r0hitrajesh/arys-rohitrajesh-footpeg-fea/CAD/v1 Top View.png

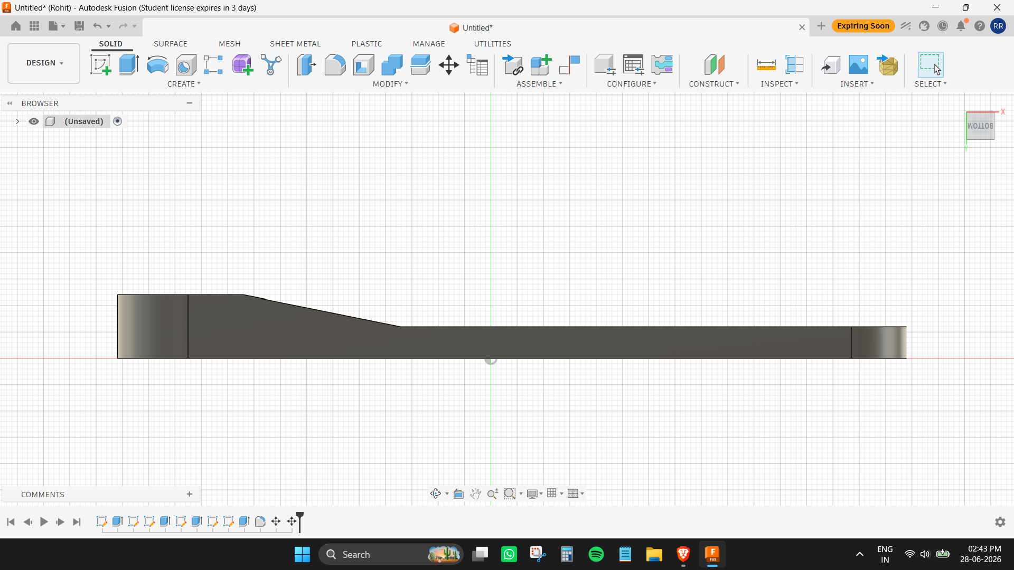
CAD/v1 Top View.png
