r0hitrajesh/arys-rohitrajesh-footpeg-fea/CAD/v2 Side View.png

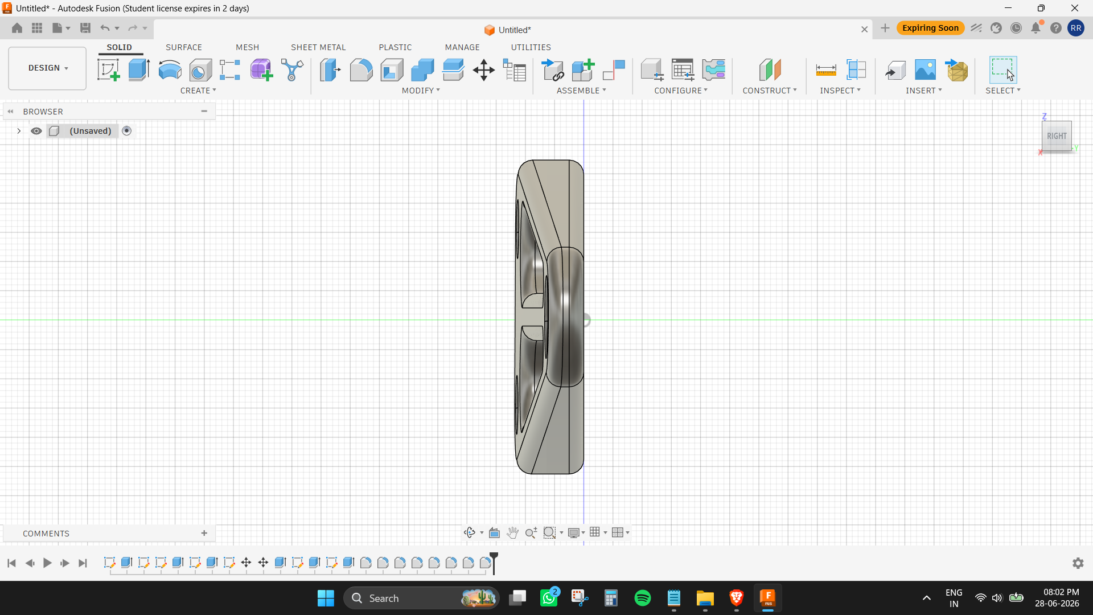
CAD/v2 Side View.png
