r0hitrajesh/arys-rohitrajesh-footpeg-fea/FEA/Displacement/Front.png

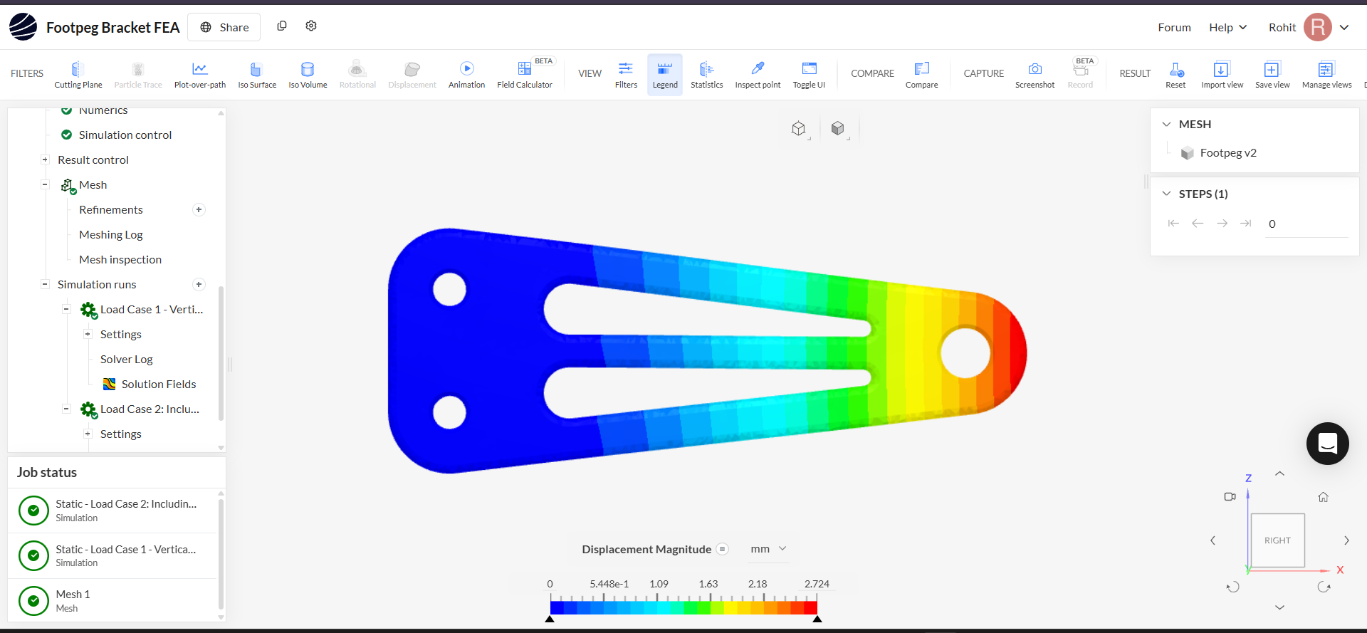
FEA/Displacement/Front.png
